LameIzuku/Hakai/site/assets/back.png

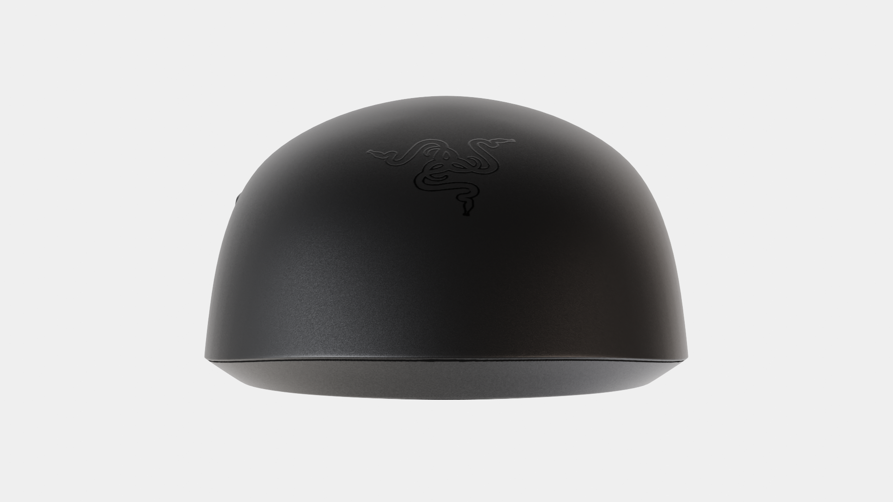
site/assets/back.png
