LameIzuku/Hakai/site/assets/diffuse-white.png

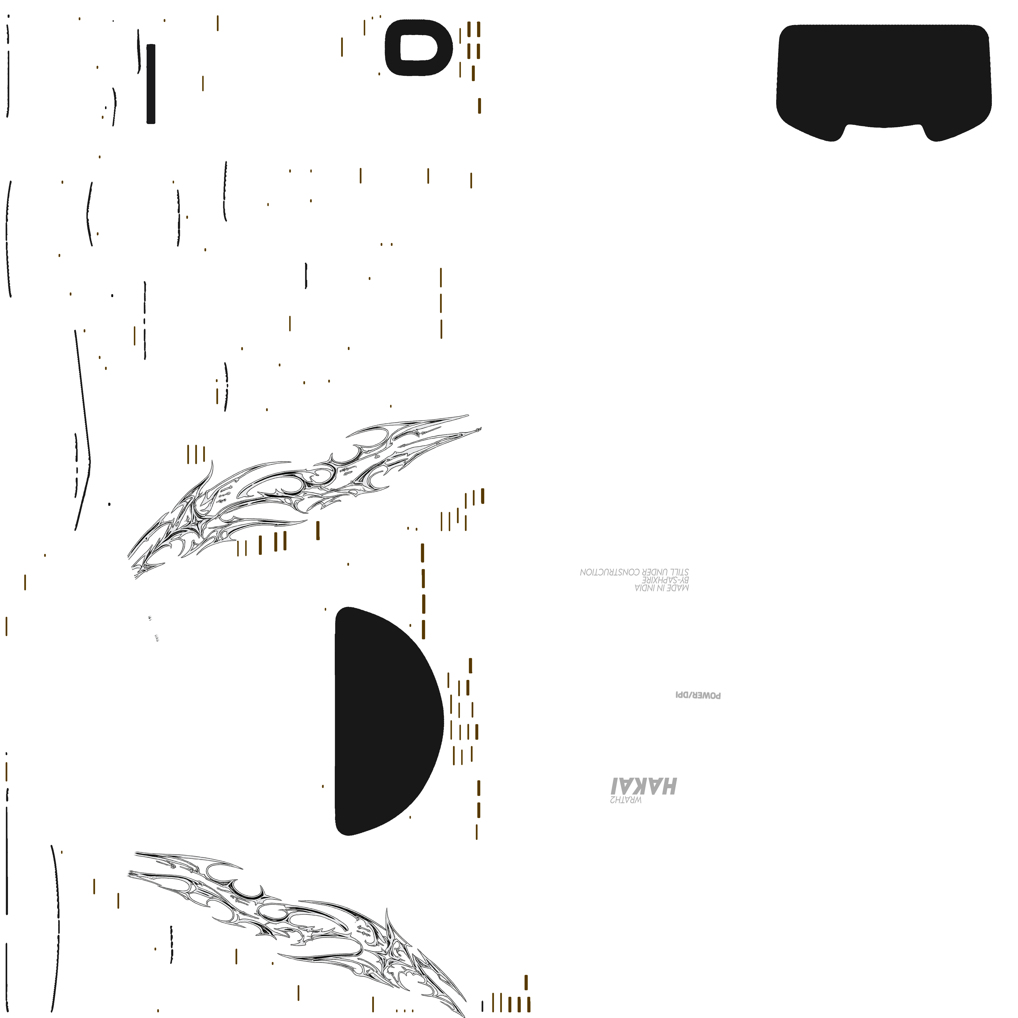
site/assets/diffuse-white.png
