LameIzuku/Hakai/site/assets/diffuse.png

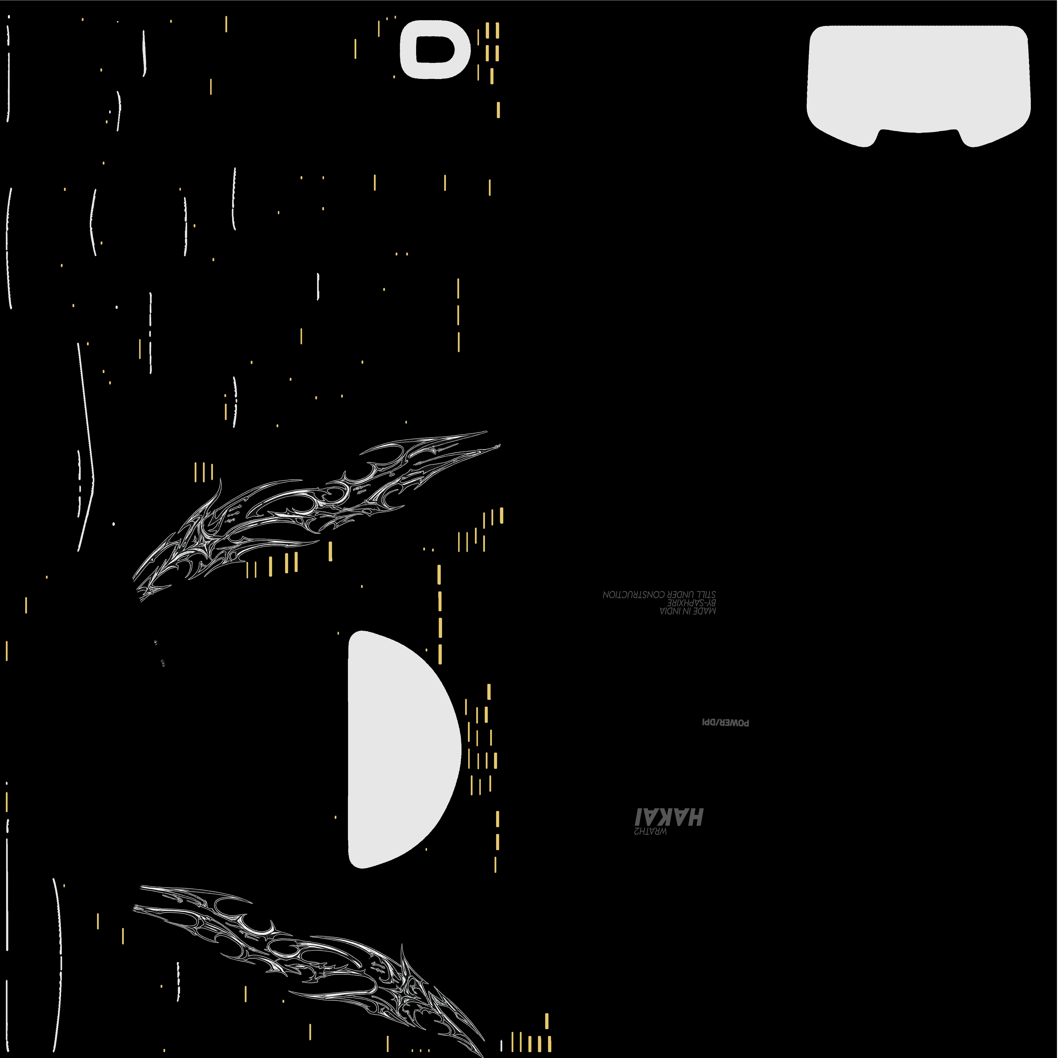
site/assets/diffuse.png
