LameIzuku/Hakai/site/assets/front.png

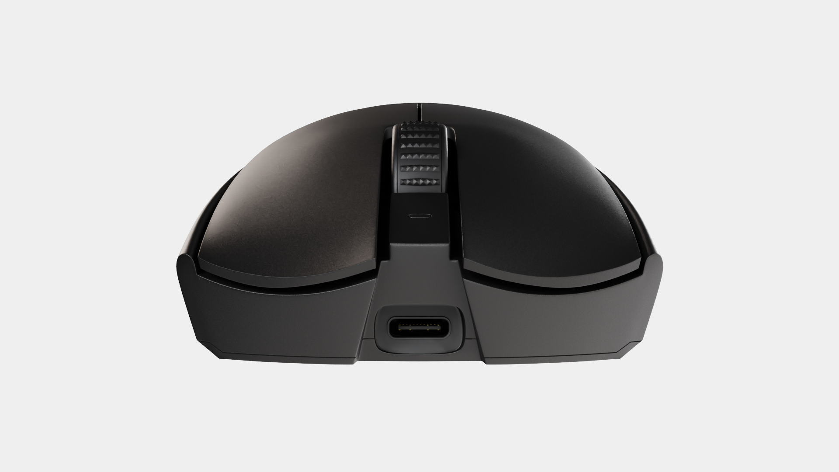
site/assets/front.png
