LameIzuku/Hakai/site/assets/left.png

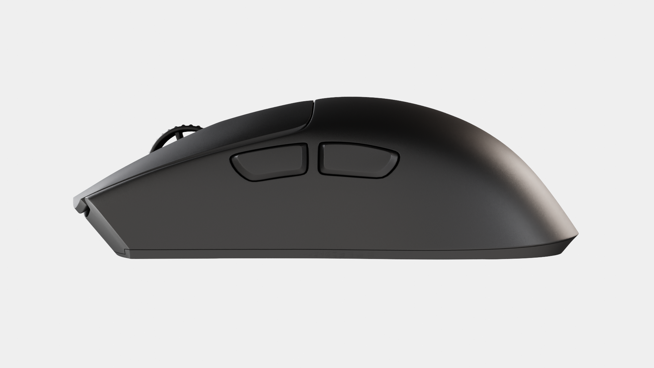
site/assets/left.png
