LameIzuku/Hakai/site/assets/roughness.png

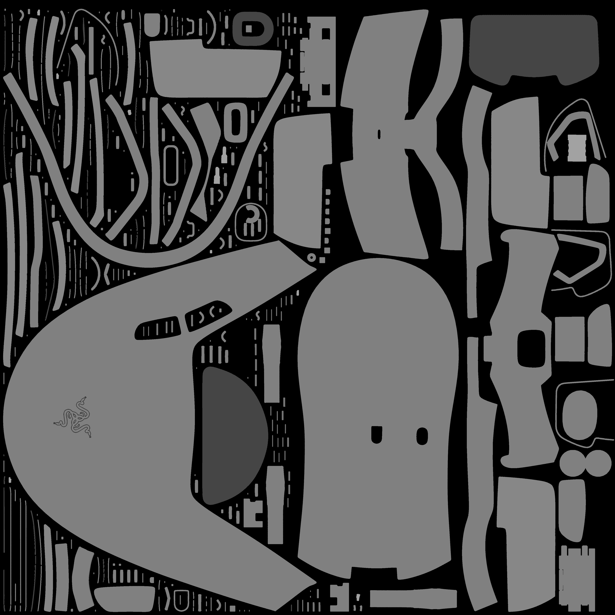
site/assets/roughness.png
