LameIzuku/Hakai/site/assets/top.png

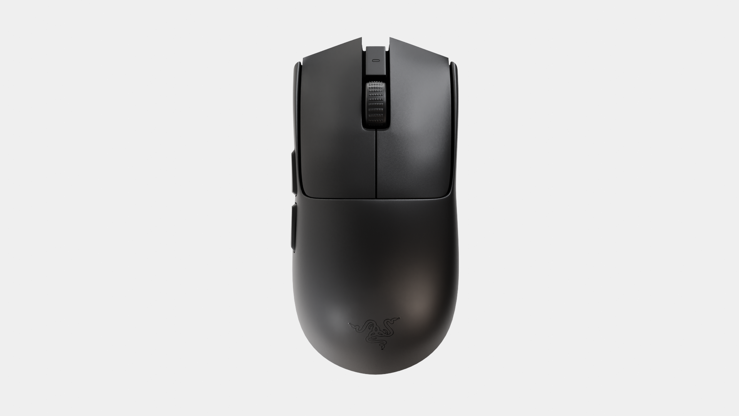
site/assets/top.png
